kenyoshizoe/ember/firmware/ember/Core/Src/adc.c

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
/* Includes ------------------------------------------------------------------*/
#include "adc.h"

ADC_HandleTypeDef hadc1;
ADC_HandleTypeDef hadc2;
ADC_HandleTypeDef hadc3;
ADC_HandleTypeDef hadc4;
DMA_HandleTypeDef hdma_adc1;
DMA_HandleTypeDef hdma_adc2;
DMA_HandleTypeDef hdma_adc3;
DMA_HandleTypeDef hdma_adc4;

/* ADC1 init function */
void MX_ADC1_Init(void)
{

  ADC_MultiModeTypeDef multimode = {0};
  ADC_ChannelConfTypeDef sConfig = {0};

  /** Common config
  */
  hadc1.Instance = ADC1;
  hadc1.Init.ClockPrescaler = ADC_CLOCK_SYNC_PCLK_DIV1;
  hadc1.Init.Resolution = ADC_RESOLUTION_12B;
  hadc1.Init.ScanConvMode = ADC_SCAN_DISABLE;
  hadc1.Init.ContinuousConvMode = DISABLE;
  hadc1.Init.DiscontinuousConvMode = DISABLE;
  hadc1.Init.ExternalTrigConvEdge = ADC_EXTERNALTRIGCONVEDGE_NONE;
  hadc1.Init.ExternalTrigConv = ADC_SOFTWARE_START;
  hadc1.Init.DataAlign = ADC_DATAALIGN_RIGHT;
  hadc1.Init.NbrOfConversion = 1;
  hadc1.Init.DMAContinuousRequests = DISABLE;
  hadc1.Init.EOCSelection = ADC_EOC_SINGLE_CONV;
  hadc1.Init.LowPowerAutoWait = DISABLE;
  hadc1.Init.Overrun = ADC_OVR_DATA_OVERWRITTEN;
  if (HAL_ADC_Init(&hadc1) != HAL_OK)
  {
    Error_Handler();
  }

  /** Configure the ADC multi-mode
  */
  multimode.Mode = ADC_DUALMODE_REGSIMULT;
  multimode.DMAAccessMode = ADC_DMAACCESSMODE_12_10_BITS;
  multimode.TwoSamplingDelay = ADC_TWOSAMPLINGDELAY_1CYCLE;
  if (HAL_ADCEx_MultiModeConfigChannel(&hadc1, &multimode) != HAL_OK)
  {
    Error_Handler();
  }

  /** Configure Regular Channel
  */
  sConfig.Channel = ADC_CHANNEL_4;
  sConfig.Rank = ADC_REGULAR_RANK_1;
  sConfig.SingleDiff = ADC_SINGLE_ENDED;
  sConfig.SamplingTime = ADC_SAMPLETIME_7CYCLES_5;
  sConfig.OffsetNumber = ADC_OFFSET_NONE;
  sConfig.Offset = 0;
  if (HAL_ADC_ConfigChannel(&hadc1, &sConfig) != HAL_OK)
  {
    Error_Handler();
  }
}
/* ADC2 init function */
void MX_ADC2_Init(void)
{

  ADC_ChannelConfTypeDef sConfig = {0};

  /** Common config
  */
  hadc2.Instance = ADC2;
  hadc2.Init.ClockPrescaler = ADC_CLOCK_SYNC_PCLK_DIV1;
  hadc2.Init.Resolution = ADC_RESOLUTION_12B;
  hadc2.Init.ScanConvMode = ADC_SCAN_DISABLE;
  hadc2.Init.ContinuousConvMode = DISABLE;
  hadc2.Init.DiscontinuousConvMode = DISABLE;
  hadc2.Init.DataAlign = ADC_DATAALIGN_RIGHT;
  hadc2.Init.NbrOfConversion = 1;
  hadc2.Init.DMAContinuousRequests = DISABLE;
  hadc2.Init.EOCSelection = ADC_EOC_SINGLE_CONV;
  hadc2.Init.LowPowerAutoWait = DISABLE;
  hadc2.Init.Overrun = ADC_OVR_DATA_OVERWRITTEN;
  if (HAL_ADC_Init(&hadc2) != HAL_OK)
  {
    Error_Handler();
  }

  /** Configure Regular Channel
  */
  sConfig.Channel = ADC_CHANNEL_1;
  sConfig.Rank = ADC_REGULAR_RANK_1;
  sConfig.SingleDiff = ADC_SINGLE_ENDED;
  sConfig.SamplingTime = ADC_SAMPLETIME_7CYCLES_5;
  sConfig.OffsetNumber = ADC_OFFSET_NONE;
  sConfig.Offset = 0;
  if (HAL_ADC_ConfigChannel(&hadc2, &sConfig) != HAL_OK)
  {
    Error_Handler();
  }
}
/* ADC3 init function */
void MX_ADC3_Init(void)
{

  ADC_MultiModeTypeDef multimode = {0};
  ADC_ChannelConfTypeDef sConfig = {0};

  /** Common config
  */
  hadc3.Instance = ADC3;
  hadc3.Init.ClockPrescaler = ADC_CLOCK_SYNC_PCLK_DIV1;
  hadc3.Init.Resolution = ADC_RESOLUTION_12B;
  hadc3.Init.ScanConvMode = ADC_SCAN_DISABLE;
  hadc3.Init.ContinuousConvMode = DISABLE;
  hadc3.Init.DiscontinuousConvMode = DISABLE;
  hadc3.Init.ExternalTrigConvEdge = ADC_EXTERNALTRIGCONVEDGE_NONE;
  hadc3.Init.ExternalTrigConv = ADC_SOFTWARE_START;
  hadc3.Init.DataAlign = ADC_DATAALIGN_RIGHT;
  hadc3.Init.NbrOfConversion = 1;
  hadc3.Init.DMAContinuousRequests = DISABLE;
  hadc3.Init.EOCSelection = ADC_EOC_SINGLE_CONV;
  hadc3.Init.LowPowerAutoWait = DISABLE;
  hadc3.Init.Overrun = ADC_OVR_DATA_OVERWRITTEN;
  if (HAL_ADC_Init(&hadc3) != HAL_OK)
  {
    Error_Handler();
  }

  /** Configure the ADC multi-mode
  */
  multimode.Mode = ADC_DUALMODE_REGSIMULT;
  multimode.DMAAccessMode = ADC_DMAACCESSMODE_12_10_BITS;
  multimode.TwoSamplingDelay = ADC_TWOSAMPLINGDELAY_1CYCLE;
  if (HAL_ADCEx_MultiModeConfigChannel(&hadc3, &multimode) != HAL_OK)
  {
    Error_Handler();
  }

  /** Configure Regular Channel
  */
  sConfig.Channel = ADC_CHANNEL_5;
  sConfig.Rank = ADC_REGULAR_RANK_1;
  sConfig.SingleDiff = ADC_SINGLE_ENDED;
  sConfig.SamplingTime = ADC_SAMPLETIME_7CYCLES_5;
  sConfig.OffsetNumber = ADC_OFFSET_NONE;
  sConfig.Offset = 0;
  if (HAL_ADC_ConfigChannel(&hadc3, &sConfig) != HAL_OK)
  {
    Error_Handler();
  }
}
/* ADC4 init function */
void MX_ADC4_Init(void)
{

  ADC_ChannelConfTypeDef sConfig = {0};

  /** Common config
  */
  hadc4.Instance = ADC4;
  hadc4.Init.ClockPrescaler = ADC_CLOCK_SYNC_PCLK_DIV1;
  hadc4.Init.Resolution = ADC_RESOLUTION_12B;
  hadc4.Init.ScanConvMode = ADC_SCAN_DISABLE;
  hadc4.Init.ContinuousConvMode = DISABLE;
  hadc4.Init.DiscontinuousConvMode = DISABLE;
  hadc4.Init.DataAlign = ADC_DATAALIGN_RIGHT;
  hadc4.Init.NbrOfConversion = 1;
  hadc4.Init.DMAContinuousRequests = DISABLE;
  hadc4.Init.EOCSelection = ADC_EOC_SINGLE_CONV;
  hadc4.Init.LowPowerAutoWait = DISABLE;
  hadc4.Init.Overrun = ADC_OVR_DATA_OVERWRITTEN;
  if (HAL_ADC_Init(&hadc4) != HAL_OK)
  {
    Error_Handler();
  }

  /** Configure Regular Channel
  */
  sConfig.Channel = ADC_CHANNEL_4;
  sConfig.Rank = ADC_REGULAR_RANK_1;
  sConfig.SingleDiff = ADC_SINGLE_ENDED;
  sConfig.SamplingTime = ADC_SAMPLETIME_7CYCLES_5;
  sConfig.OffsetNumber = ADC_OFFSET_NONE;
  sConfig.Offset = 0;
  if (HAL_ADC_ConfigChannel(&hadc4, &sConfig) != HAL_OK)
  {
    Error_Handler();
  }
}

static uint32_t HAL_RCC_ADC12_CLK_ENABLED=0;
static uint32_t HAL_RCC_ADC34_CLK_ENABLED=0;

void HAL_ADC_MspInit(ADC_HandleTypeDef* adcHandle)
{

  GPIO_InitTypeDef GPIO_InitStruct = {0};
  if(adcHandle->Instance==ADC1)
  {
    /* ADC1 clock enable */
    HAL_RCC_ADC12_CLK_ENABLED++;
    if(HAL_RCC_ADC12_CLK_ENABLED==1){
      __HAL_RCC_ADC12_CLK_ENABLE();
    }

    __HAL_RCC_GPIOA_CLK_ENABLE();
    /**ADC1 GPIO Configuration
    PA3     ------> ADC1_IN4
    */
    GPIO_InitStruct.Pin = GPIO_PIN_3;
    GPIO_InitStruct.Mode = GPIO_MODE_ANALOG;
    GPIO_InitStruct.Pull = GPIO_NOPULL;
    HAL_GPIO_Init(GPIOA, &GPIO_InitStruct);

    /* ADC1 DMA Init */
    /* ADC1 Init */
    hdma_adc1.Instance = DMA1_Channel1;
    hdma_adc1.Init.Direction = DMA_PERIPH_TO_MEMORY;
    hdma_adc1.Init.PeriphInc = DMA_PINC_DISABLE;
    hdma_adc1.Init.MemInc = DMA_MINC_ENABLE;
    hdma_adc1.Init.PeriphDataAlignment = DMA_PDATAALIGN_WORD;
    hdma_adc1.Init.MemDataAlignment = DMA_MDATAALIGN_WORD;
    hdma_adc1.Init.Mode = DMA_CIRCULAR;
    hdma_adc1.Init.Priority = DMA_PRIORITY_LOW;
    if (HAL_DMA_Init(&hdma_adc1) != HAL_OK)
    {
      Error_Handler();
    }

    __HAL_LINKDMA(adcHandle,DMA_Handle,hdma_adc1);

    /* ADC1 interrupt Init */
    HAL_NVIC_SetPriority(ADC1_2_IRQn, 0, 0);
    HAL_NVIC_EnableIRQ(ADC1_2_IRQn);
  }
  else if(adcHandle->Instance==ADC2)
  {
    /* ADC2 clock enable */
    HAL_RCC_ADC12_CLK_ENABLED++;
    if(HAL_RCC_ADC12_CLK_ENABLED==1){
      __HAL_RCC_ADC12_CLK_ENABLE();
    }

    __HAL_RCC_GPIOA_CLK_ENABLE();
    /**ADC2 GPIO Configuration
    PA4     ------> ADC2_IN1
    */
    GPIO_InitStruct.Pin = GPIO_PIN_4;
    GPIO_InitStruct.Mode = GPIO_MODE_ANALOG;
    GPIO_InitStruct.Pull = GPIO_NOPULL;
    HAL_GPIO_Init(GPIOA, &GPIO_InitStruct);

    /* ADC2 DMA Init */
    /* ADC2 Init */
    hdma_adc2.Instance = DMA2_Channel1;
    hdma_adc2.Init.Direction = DMA_PERIPH_TO_MEMORY;
    hdma_adc2.Init.PeriphInc = DMA_PINC_DISABLE;
    hdma_adc2.Init.MemInc = DMA_MINC_ENABLE;
    hdma_adc2.Init.PeriphDataAlignment = DMA_PDATAALIGN_WORD;
    hdma_adc2.Init.MemDataAlignment = DMA_MDATAALIGN_WORD;
    hdma_adc2.Init.Mode = DMA_CIRCULAR;
    hdma_adc2.Init.Priority = DMA_PRIORITY_LOW;
    if (HAL_DMA_Init(&hdma_adc2) != HAL_OK)
    {
      Error_Handler();
    }

    __HAL_LINKDMA(adcHandle,DMA_Handle,hdma_adc2);

    /* ADC2 interrupt Init */
    HAL_NVIC_SetPriority(ADC1_2_IRQn, 0, 0);
    HAL_NVIC_EnableIRQ(ADC1_2_IRQn);
  }
  else if(adcHandle->Instance==ADC3)
  {
    /* ADC3 clock enable */
    HAL_RCC_ADC34_CLK_ENABLED++;
    if(HAL_RCC_ADC34_CLK_ENABLED==1){
      __HAL_RCC_ADC34_CLK_ENABLE();
    }

    __HAL_RCC_GPIOB_CLK_ENABLE();
    /**ADC3 GPIO Configuration
    PB13     ------> ADC3_IN5
    */
    GPIO_InitStruct.Pin = GPIO_PIN_13;
    GPIO_InitStruct.Mode = GPIO_MODE_ANALOG;
    GPIO_InitStruct.Pull = GPIO_NOPULL;
    HAL_GPIO_Init(GPIOB, &GPIO_InitStruct);

    /* ADC3 DMA Init */
    /* ADC3 Init */
    hdma_adc3.Instance = DMA2_Channel5;
    hdma_adc3.Init.Direction = DMA_PERIPH_TO_MEMORY;
    hdma_adc3.Init.PeriphInc = DMA_PINC_DISABLE;
    hdma_adc3.Init.MemInc = DMA_MINC_ENABLE;
    hdma_adc3.Init.PeriphDataAlignment = DMA_PDATAALIGN_WORD;
    hdma_adc3.Init.MemDataAlignment = DMA_MDATAALIGN_WORD;
    hdma_adc3.Init.Mode = DMA_CIRCULAR;
    hdma_adc3.Init.Priority = DMA_PRIORITY_LOW;
    if (HAL_DMA_Init(&hdma_adc3) != HAL_OK)
    {
      Error_Handler();
    }

    __HAL_LINKDMA(adcHandle,DMA_Handle,hdma_adc3);

    /* ADC3 interrupt Init */
    HAL_NVIC_SetPriority(ADC3_IRQn, 0, 0);
    HAL_NVIC_EnableIRQ(ADC3_IRQn);
  }
  else if(adcHandle->Instance==ADC4)
  {
    /* ADC4 clock enable */
    HAL_RCC_ADC34_CLK_ENABLED++;
    if(HAL_RCC_ADC34_CLK_ENABLED==1){
      __HAL_RCC_ADC34_CLK_ENABLE();
    }

    __HAL_RCC_GPIOB_CLK_ENABLE();
    /**ADC4 GPIO Configuration
    PB14     ------> ADC4_IN4
    */
    GPIO_InitStruct.Pin = GPIO_PIN_14;
    GPIO_InitStruct.Mode = GPIO_MODE_ANALOG;
    GPIO_InitStruct.Pull = GPIO_NOPULL;
    HAL_GPIO_Init(GPIOB, &GPIO_InitStruct);

    /* ADC4 DMA Init */
    /* ADC4 Init */
    hdma_adc4.Instance = DMA2_Channel2;
    hdma_adc4.Init.Direction = DMA_PERIPH_TO_MEMORY;
    hdma_adc4.Init.PeriphInc = DMA_PINC_DISABLE;
    hdma_adc4.Init.MemInc = DMA_MINC_ENABLE;
    hdma_adc4.Init.PeriphDataAlignment = DMA_PDATAALIGN_WORD;
    hdma_adc4.Init.MemDataAlignment = DMA_MDATAALIGN_WORD;
    hdma_adc4.Init.Mode = DMA_CIRCULAR;
    hdma_adc4.Init.Priority = DMA_PRIORITY_LOW;
    if (HAL_DMA_Init(&hdma_adc4) != HAL_OK)
    {
      Error_Handler();
    }

    __HAL_LINKDMA(adcHandle,DMA_Handle,hdma_adc4);

    /* ADC4 interrupt Init */
    HAL_NVIC_SetPriority(ADC4_IRQn, 0, 0);
    HAL_NVIC_EnableIRQ(ADC4_IRQn);
  }
}

void HAL_ADC_MspDeInit(ADC_HandleTypeDef* adcHandle)
{

  if(adcHandle->Instance==ADC1)
  {
    /* Peripheral clock disable */
    HAL_RCC_ADC12_CLK_ENABLED--;
    if(HAL_RCC_ADC12_CLK_ENABLED==0){
      __HAL_RCC_ADC12_CLK_DISABLE();
    }

    /**ADC1 GPIO Configuration
    PA3     ------> ADC1_IN4
    */
    HAL_GPIO_DeInit(GPIOA, GPIO_PIN_3);

    /* ADC1 DMA DeInit */
    HAL_DMA_DeInit(adcHandle->DMA_Handle);

    /* ADC1 interrupt Deinit */
  /* USER CODE BEGIN ADC1:ADC1_2_IRQn disable */
    /**
    * Uncomment the line below to disable the "ADC1_2_IRQn" interrupt
    * Be aware, disabling shared interrupt may affect other IPs
    */
    /* HAL_NVIC_DisableIRQ(ADC1_2_IRQn); */
  /* USER CODE END ADC1:ADC1_2_IRQn disable */

  }
  else if(adcHandle->Instance==ADC2)
  {
    /* Peripheral clock disable */
    HAL_RCC_ADC12_CLK_ENABLED--;
    if(HAL_RCC_ADC12_CLK_ENABLED==0){
      __HAL_RCC_ADC12_CLK_DISABLE();
    }

    /**ADC2 GPIO Configuration
    PA4     ------> ADC2_IN1
    */
    HAL_GPIO_DeInit(GPIOA, GPIO_PIN_4);

    /* ADC2 DMA DeInit */
    HAL_DMA_DeInit(adcHandle->DMA_Handle);

    /* ADC2 interrupt Deinit */
  /* USER CODE BEGIN ADC2:ADC1_2_IRQn disable */
    /**
    * Uncomment the line below to disable the "ADC1_2_IRQn" interrupt
    * Be aware, disabling shared interrupt may affect other IPs
    */
    /* HAL_NVIC_DisableIRQ(ADC1_2_IRQn); */
  /* USER CODE END ADC2:ADC1_2_IRQn disable */

  }
  else if(adcHandle->Instance==ADC3)
  {
    /* Peripheral clock disable */
    HAL_RCC_ADC34_CLK_ENABLED--;
    if(HAL_RCC_ADC34_CLK_ENABLED==0){
      __HAL_RCC_ADC34_CLK_DISABLE();
    }

    /**ADC3 GPIO Configuration
    PB13     ------> ADC3_IN5
    */
    HAL_GPIO_DeInit(GPIOB, GPIO_PIN_13);

    /* ADC3 DMA DeInit */
    HAL_DMA_DeInit(adcHandle->DMA_Handle);

    /* ADC3 interrupt Deinit */
    HAL_NVIC_DisableIRQ(ADC3_IRQn);
  }
  else if(adcHandle->Instance==ADC4)
  {
    /* Peripheral clock disable */
    HAL_RCC_ADC34_CLK_ENABLED--;
    if(HAL_RCC_ADC34_CLK_ENABLED==0){
      __HAL_RCC_ADC34_CLK_DISABLE();
    }

    /**ADC4 GPIO Configuration
    PB14     ------> ADC4_IN4
    */
    HAL_GPIO_DeInit(GPIOB, GPIO_PIN_14);

    /* ADC4 DMA DeInit */
    HAL_DMA_DeInit(adcHandle->DMA_Handle);

    /* ADC4 interrupt Deinit */
    HAL_NVIC_DisableIRQ(ADC4_IRQn);
  }
}
