kenyoshizoe/ember/firmware/ember/src/app/usb_descriptors.cc

/*
 * The MIT License (MIT)
 *
 * Copyright (c) 2019 Ha Thach (tinyusb.org)
 *
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
 */

#include "usb_descriptors.h"

#include "tusb.h"

/* A combination of interfaces must have a unique product id, since PC will save
 * device driver after the first plug. Same VID/PID with different interface e.g
 * MSC (first), then CDC (later) will possibly cause system error on PC.
 *
 * Auto ProductID layout's Bitmap:
 *   [MSB]         HID | MSC | CDC          [LSB]
 */
#define _PID_MAP(itf, n) ((CFG_TUD_##itf) << (n))
#define USB_PID                                                      \
  (0x4000 | _PID_MAP(CDC, 0) | _PID_MAP(MSC, 1) | _PID_MAP(HID, 2) | \
   _PID_MAP(MIDI, 3) | _PID_MAP(VENDOR, 4))

//--------------------------------------------------------------------+
// Device Descriptors
//--------------------------------------------------------------------+
tusb_desc_device_t const desc_device = {
    .bLength = sizeof(tusb_desc_device_t),
    .bDescriptorType = TUSB_DESC_DEVICE,
    .bcdUSB = 0x0200,

    .bDeviceClass = TUSB_CLASS_MISC,
    .bDeviceSubClass = MISC_SUBCLASS_COMMON,
    .bDeviceProtocol = MISC_PROTOCOL_IAD,
    .bMaxPacketSize0 = CFG_TUD_ENDPOINT0_SIZE,

    .idVendor = 0xCafe,
    .idProduct = USB_PID,
    .bcdDevice = 0x0100,

    .iManufacturer = 0x01,
    .iProduct = 0x02,
    .iSerialNumber = 0x03,

    .bNumConfigurations = 0x01};

// Invoked when received GET DEVICE DESCRIPTOR
// Application return pointer to descriptor
uint8_t const* tud_descriptor_device_cb(void) {
  return (uint8_t const*)&desc_device;
}

//--------------------------------------------------------------------+
// HID Report Descriptor
//--------------------------------------------------------------------+

uint8_t const desc_hid_report[] = {TUD_HID_REPORT_DESC_KEYBOARD()};

// Invoked when received GET HID REPORT DESCRIPTOR
// Application return pointer to descriptor
// Descriptor contents must exist long enough for transfer to complete
uint8_t const* tud_hid_descriptor_report_cb(uint8_t itf) {
  (void)itf;
  return desc_hid_report;
}

//--------------------------------------------------------------------+
// Configuration Descriptor
//--------------------------------------------------------------------+

enum {
  ITF_NUM_CDC = 0,
  ITF_NUM_CDC_DATA,
  ITF_NUM_HID,
  ITF_NUM_MIDI,
  ITF_NUM_MIDI_STREAMING,
  ITF_NUM_TOTAL
};

#define EPNUM_CDC_NOTIF 0x81
#define EPNUM_CDC_OUT 0x02
#define EPNUM_CDC_IN 0x82
#define EPNUM_HID 0x85
#define EPNUM_MIDI_OUT 0x03
#define EPNUM_MIDI_IN 0x83

#define CONFIG_TOTAL_LEN                                       \
  (TUD_CONFIG_DESC_LEN + TUD_CDC_DESC_LEN + TUD_HID_DESC_LEN + \
   TUD_MIDI_DESC_LEN)

uint8_t const desc_configuration[] = {
    // Config number, interface count, string index, total length, attribute,
    // power in mA
    TUD_CONFIG_DESCRIPTOR(1, ITF_NUM_TOTAL, 0, CONFIG_TOTAL_LEN, 0x00, 100),
    // Interface number, string index, EP notification address and size, EP data
    // address (out, in) and size.
    TUD_CDC_DESCRIPTOR(ITF_NUM_CDC, 4, EPNUM_CDC_NOTIF, 8, EPNUM_CDC_OUT,
                       EPNUM_CDC_IN, 64),
    // Interface number, string index, protocol, report descriptor len, EP In
    // address, size & polling interval
    TUD_HID_DESCRIPTOR(ITF_NUM_HID, 5, HID_ITF_PROTOCOL_NONE,
                       sizeof(desc_hid_report), EPNUM_HID,
                       CFG_TUD_HID_EP_BUFSIZE, 10),
    // Interface number, string index, EP Out & EP In address, EP size
    TUD_MIDI_DESCRIPTOR(ITF_NUM_MIDI, 0, EPNUM_MIDI_OUT, EPNUM_MIDI_IN, 64)};

// Invoked when received GET CONFIGURATION DESCRIPTOR
// Application return pointer to descriptor
// Descriptor contents must exist long enough for transfer to complete
uint8_t const* tud_descriptor_configuration_cb(uint8_t index) {
  (void)index;  // for multiple configurations
  return desc_configuration;
}

//--------------------------------------------------------------------+
// String Descriptors
//--------------------------------------------------------------------+

// array of pointer to string descriptors
char const* string_desc_arr[] = {
    (const char[]){0x09, 0x04},  // 0: is supported language is English (0x0409)
    "@kenyoshizoe",              // 1: Manufacturer
    "Ember",                     // 2: Product
    "123456789012",              // 3: Serials, should use chip ID
    "Ember CDC",                 // 4: CDC Interface
    "Ember HID",                 // 5: HID Interface
};

static uint16_t _desc_str[32];

// Invoked when received GET STRING DESCRIPTOR request
// Application return pointer to descriptor, whose contents must exist long
// enough for transfer to complete
uint16_t const* tud_descriptor_string_cb(uint8_t index, uint16_t langid) {
  (void)langid;
  size_t chr_count = 0;

  if (index == 0) {
    memcpy(&_desc_str[1], string_desc_arr[0], 2);
    chr_count = 1;
  } else {
    // Note: the 0xEE index string is a Microsoft OS 1.0 Descriptors.
    // https://docs.microsoft.com/en-us/windows-hardware/drivers/usbcon/microsoft-defined-usb-descriptors

    if (!(index < sizeof(string_desc_arr) / sizeof(string_desc_arr[0])))
      return NULL;

    const char* str = string_desc_arr[index];

    // Cap at max char
    chr_count = (uint8_t)strlen(str);
    if (chr_count > 31) chr_count = 31;

    // Convert ASCII string into UTF-16
    for (uint8_t i = 0; i < chr_count; i++) {
      _desc_str[1 + i] = str[i];
    }
  }

  // first byte is length (including header), second byte is string type
  _desc_str[0] = (TUSB_DESC_STRING << 8) | (2 * chr_count + 2);

  return _desc_str;
}
